ghostaz/robotyaga/Приложение/image/Связь с роботом Зеленый.png

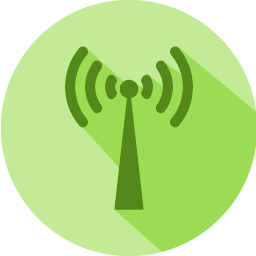
Приложение/image/Связь с роботом Зеленый.png
